tonyxforce/LynxSchematic/pcb/3v3.kicad_sch

## KiCad design pcb/3v3.kicad_sch (2026-06-30)

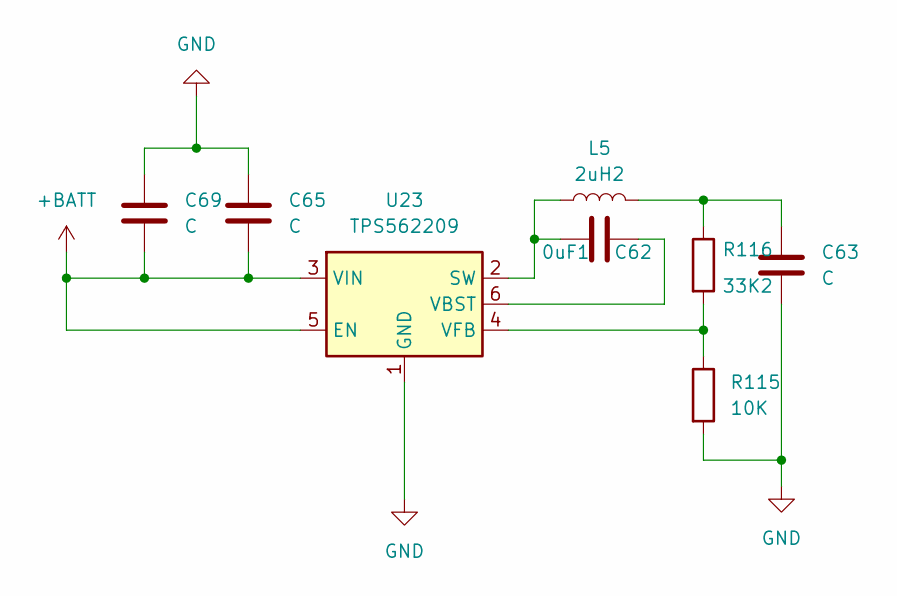
[picture p4: schematic 3v3.kicad_sch]

Parts:
C62: 0uF1
C63, C65, C69: C
L5: 2uH2
R115: 10K
R116: 33K2
U23: TPS562209; SOT-23-6

Connections:
+BATT: C65.2, C69.2, U23.3 (VIN), U23.5 (EN)
GND: C63.2, C65.1, C69.1, R115.2, U23.1 (GND)
unnamed: C62.1, L5.1, U23.2 (SW)
unnamed: C62.2, U23.6 (VBST)
unnamed: C63.1, L5.2, R116.1
unnamed: R115.1, R116.2, U23.4 (VFB)
