tonyxforce/LynxSchematic/pcb/5v.kicad_sch

## KiCad design pcb/5v.kicad_sch (2026-06-30)

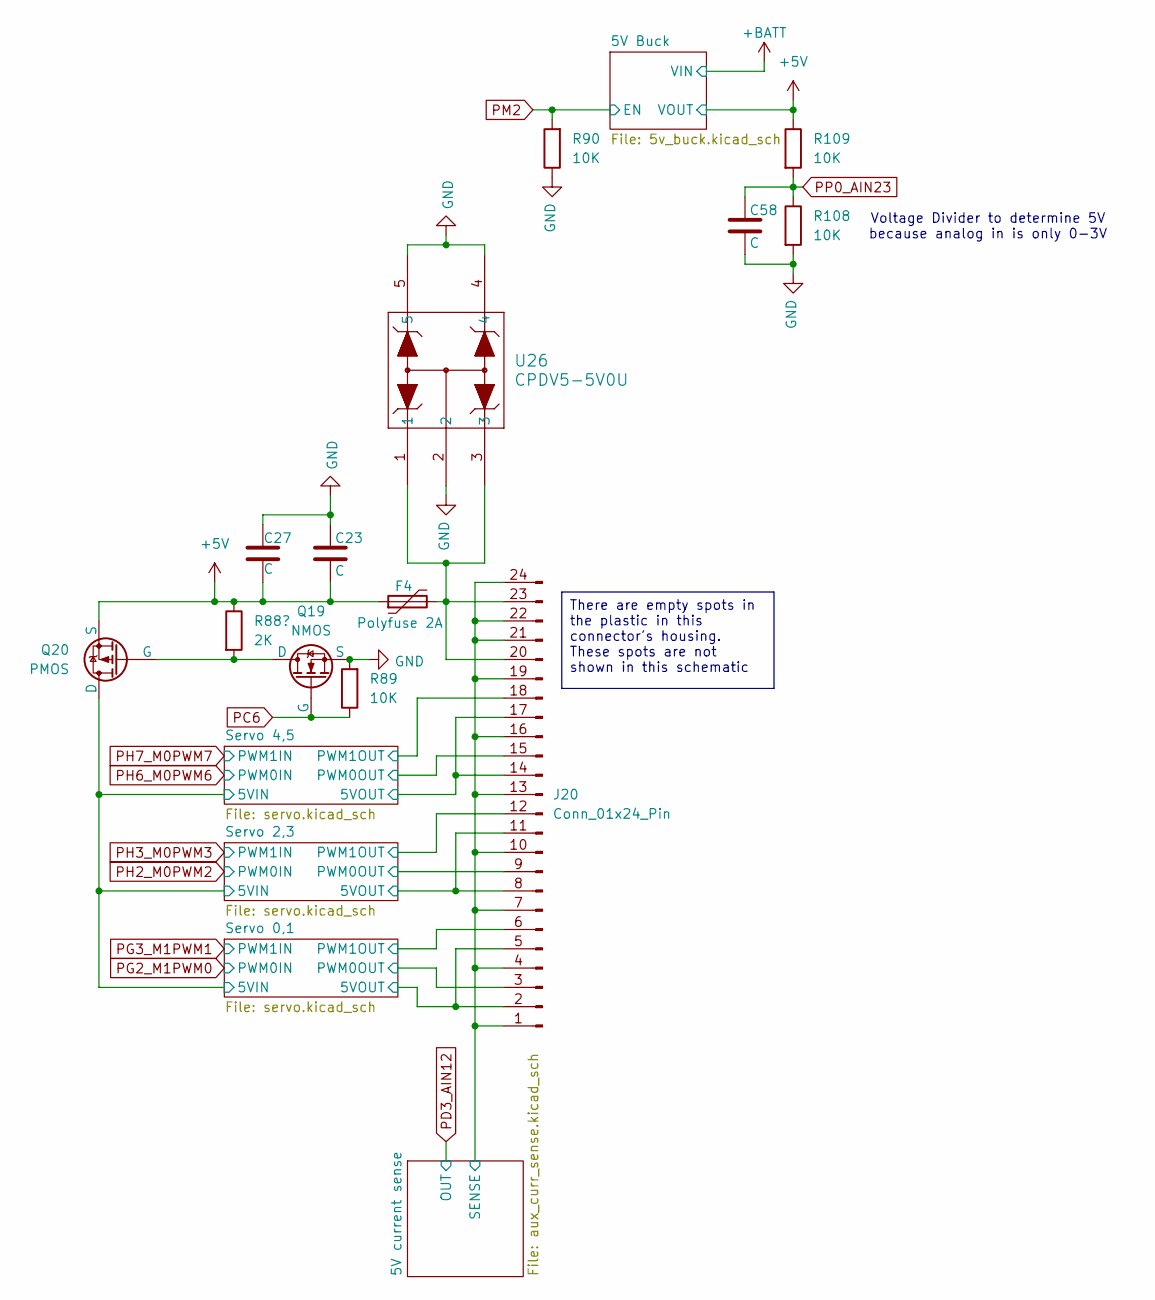
[picture p5: schematic 5v.kicad_sch]

Parts:
C23, C27, C58: C
F4: Polyfuse 2A
J20: Conn_01x24_Pin
Q19: NMOS
Q20: PMOS
R89, R90, R108, R109: 10K
U26: CPDV5-5V0U; SOT353_CPDV5_CIP

Connections:
5VIN: Q20.1 (D)
5VOUT: J20.2, J20.5, J20.8, J20.11, J20.14, J20.17
+5V: C23.2, C27.1, F4.1, Q20.3 (S), R109.1
GND: C23.1, C27.2, C58.2, Q19.3 (S), R89.2, R90.1, R108.2, U26.2, U26.4, U26.5
unnamed: F4.2, J20.20, J20.23, U26.1, U26.3
unnamed: Q19.1 (D), Q20.2 (G)
PC6: Q19.2 (G), R89.1
PM2: R90.2
PP0_AIN23: C58.1, R108.1, R109.2
PWM0OUT: J20.3, J20.9, J20.15
PWM1OUT: J20.6, J20.12, J20.18
SENSE: J20.1, J20.4, J20.7, J20.10, J20.13, J20.16, J20.19, J20.21, J20.22, J20.24

Notes on the sheet:
Voltage Divider to determine 5V because analog in is only 0-3V
There are empty spots in the plastic in this connector's housing. These spots are not shown in this schematic
