tonyxforce/LynxSchematic/pcb/5v_buck.kicad_sch

## KiCad design pcb/5v_buck.kicad_sch (2026-06-30)

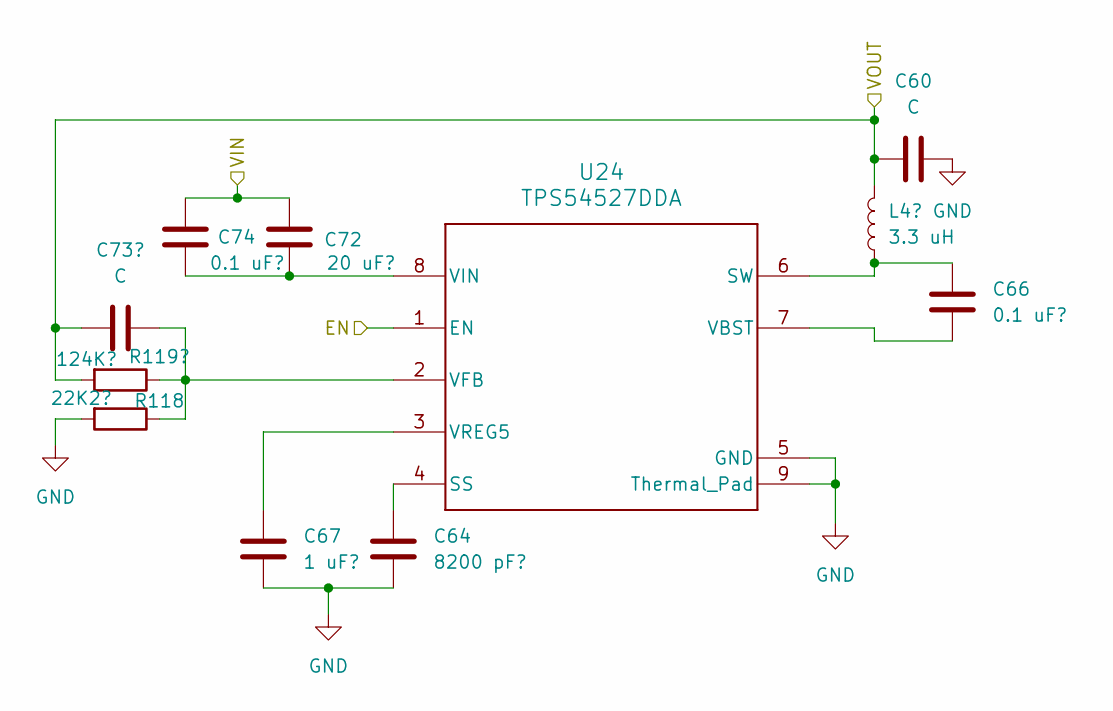
[picture p6: schematic 5v_buck.kicad_sch]

Parts:
C60: C
C64: 8200 pF?
C66, C74: 0.1 uF?
C67: 1 uF?
C72: 20 uF?
R118: 22K2?
U24: TPS54527DDA; DDA0008E-IPC_A

Connections:
EN: U24.1 (EN)
GND: C60.2, C64.2, C67.2, R118.2, U24.5 (GND), U24.9 (Thermal_Pad)
unnamed: C64.1, U24.4 (SS)
unnamed: C66.1, U24.6 (SW)
unnamed: C66.2, U24.7 (VBST)
unnamed: C67.1, U24.3 (VREG5)
unnamed: C72.2, C74.2, U24.8 (VIN)
unnamed: R118.1, U24.2 (VFB)
VIN: C72.1, C74.1
VOUT: C60.1
