tonyxforce/LynxSchematic/pcb/12v.kicad_sch

## KiCad design pcb/12v.kicad_sch (2026-06-30)

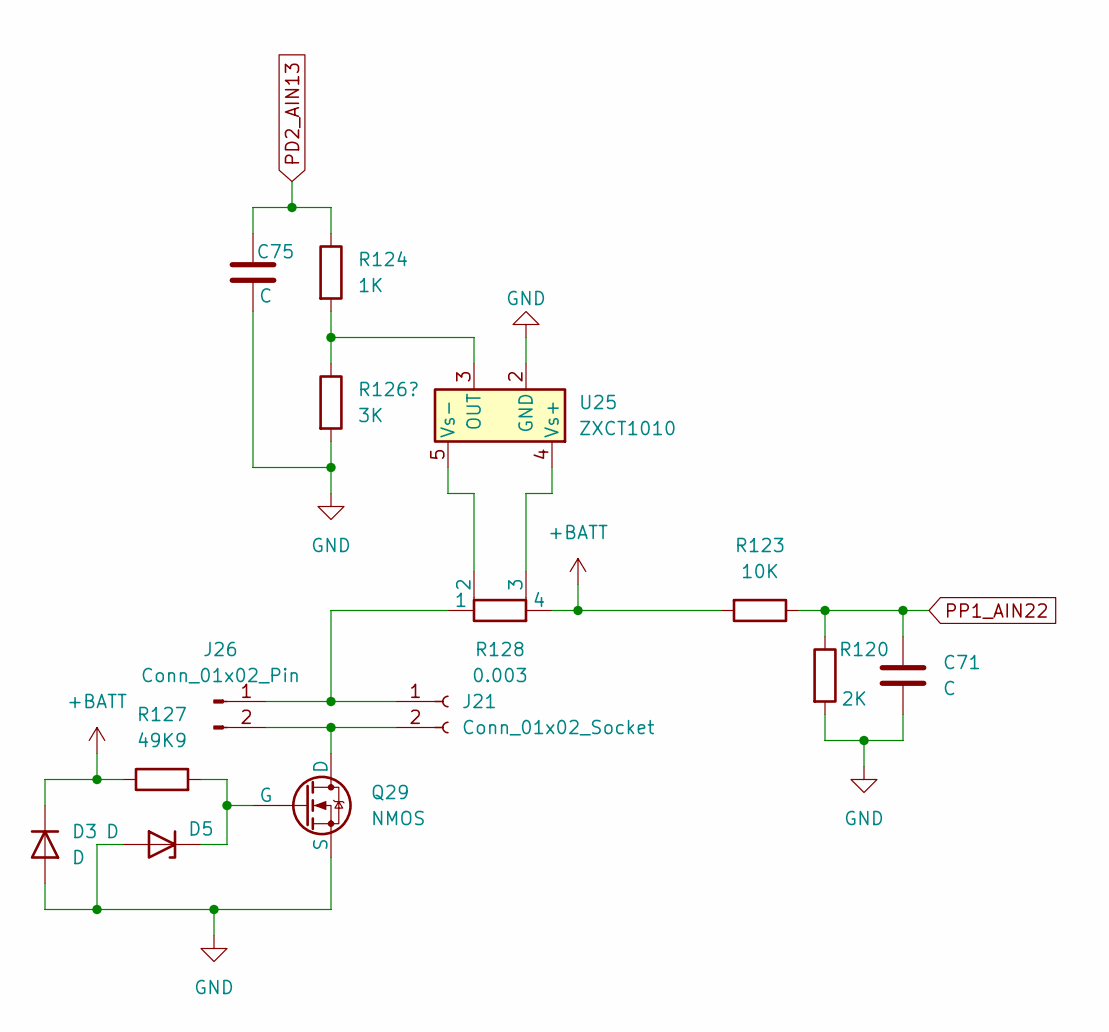
[picture p7: schematic 12v.kicad_sch]

Parts:
C71, C75: C
D3: D
D5: D; D_SOD-882
J21: Conn_01x02_Socket
J26: Conn_01x02_Pin
Q29: NMOS
R120: 2K
R123: 10K
R124: 1K
R127: 49K9
R128: 0.003
U25: ZXCT1010; SOT-23-5

Connections:
+BATT: D3.1 (K), R123.2, R127.1, R128.4
GND: C71.2, C75.1, D3.2 (A), D5.2 (A), Q29.3 (S), R120.2, U25.2 (GND)
unnamed: D5.1 (K), Q29.2 (G), R127.2
unnamed: J21.1, J26.1, R128.1
unnamed: J21.2, J26.2, Q29.1 (D)
unnamed: R124.2, U25.3 (OUT)
unnamed: R128.2, U25.5 (Vs-)
unnamed: R128.3, U25.4 (Vs+)
PD2_AIN13: C75.2, R124.1
PP1_AIN22: C71.1, R120.1, R123.1
