tonyxforce/LynxSchematic/pcb/analog_in_connector.kicad_sch

## KiCad design pcb/analog_in_connector.kicad_sch (2026-06-30)

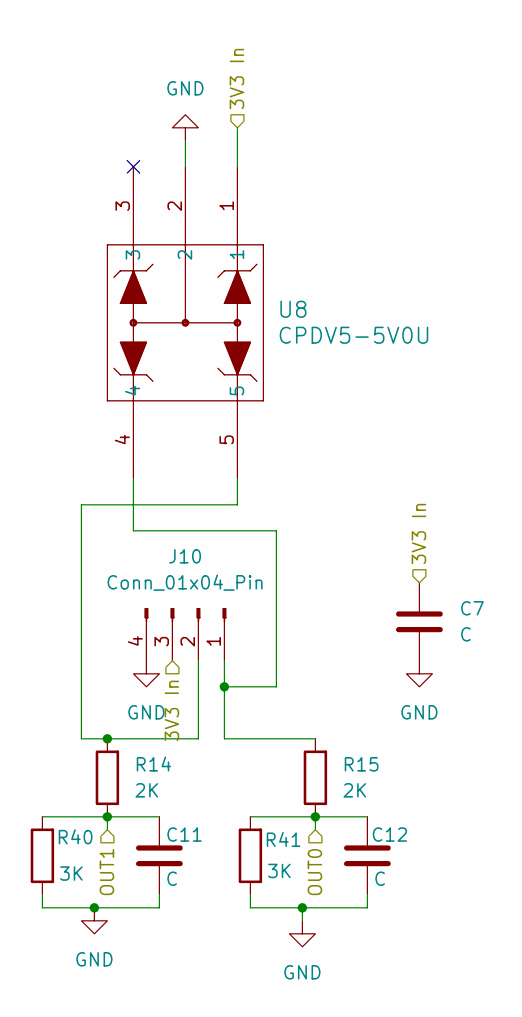
[picture p8: schematic analog_in_connector.kicad_sch]

Parts:
C7, C11, C12: C
J10: Conn_01x04_Pin
R14, R15: 2K
R40, R41: 3K
U8: CPDV5-5V0U; SOT353_CPDV5_CIP

Connections:
3V3 In: C7.1, J10.3, U8.1
GND: C7.2, C11.2, C12.2, J10.4, R40.1, R41.1, U8.2
unnamed: J10.1, R15.2, U8.4
unnamed: J10.2, R14.2, U8.5
OUT0: C12.1, R15.1, R41.2
OUT1: C11.1, R14.1, R40.2
