tonyxforce/LynxSchematic/pcb/android_header.kicad_sch

## KiCad design pcb/android_header.kicad_sch (2026-06-30)

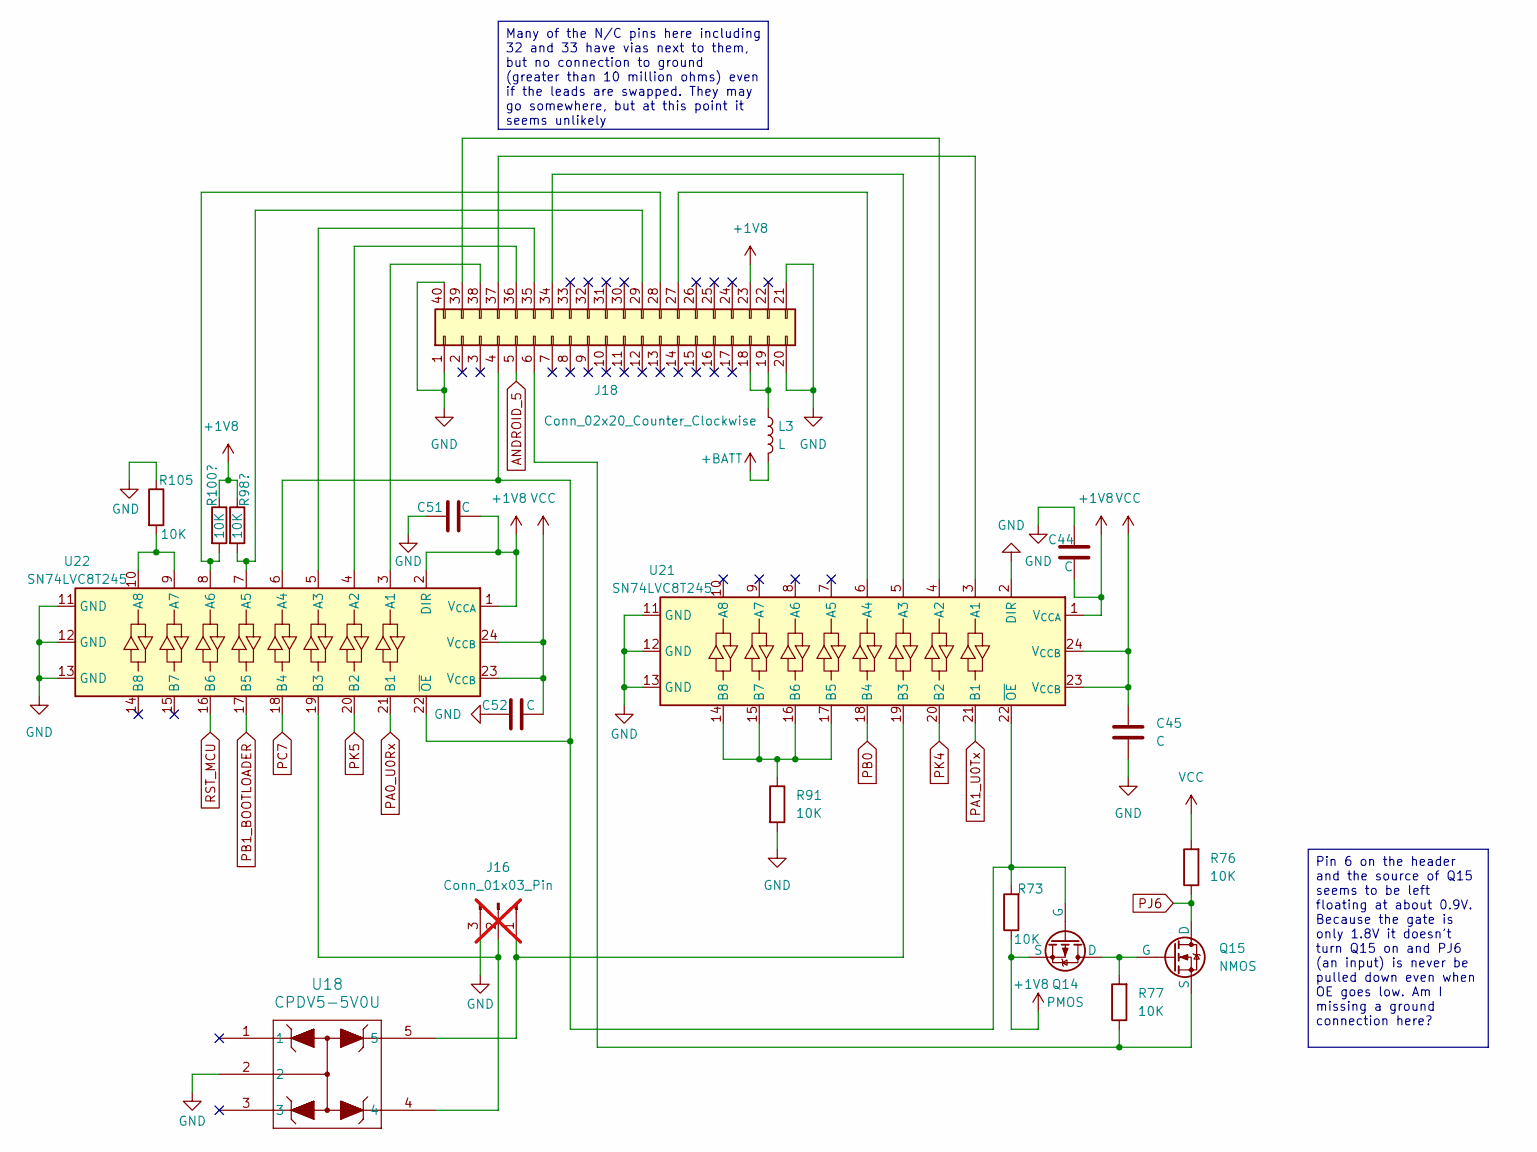
[picture p9: schematic android_header.kicad_sch]

Parts:
C44, C45, C51, C52: C
J16: Conn_01x03_Pin; not fitted
J18: Conn_02x20_Counter_Clockwise
L3: L
Q14: PMOS
Q15: NMOS
R73, R76, R77, R91, R105: 10K
U18: CPDV5-5V0U; SOT353_CPDV5_CIP
U21, U22: SN74LVC8T245

Connections:
+1V8: C44.2, C51.2, J18.23, Q14.3 (S), R73.1, U21.1 (V_{CCA}), U22.1 (V_{CCA}), U22.2 (DIR)
+BATT: L3.2
ANDROID_5: J18.5
GND: C44.1, C45.2, C51.1, C52.1, J16.3, J18.1, J18.20, J18.21, J18.40, R91.2, R105.1, U18.2, U21.2 (DIR), U21.11 (GND), U21.12 (GND), U21.13 (GND), U22.11 (GND), U22.12 (GND), U22.13 (GND)
unnamed: J16.1, U18.5, U21.19 (B3)
unnamed: J16.2, U18.4, U22.19 (B3)
unnamed: J18.4, Q14.2 (G), R73.2, U21.22 (~OE), U22.6 (A4), U22.22 (~OE)
unnamed: J18.6, Q15.3 (S), R77.1
unnamed: J18.18, J18.19, L3.1
unnamed: J18.27, U21.6 (A4)
unnamed: J18.28, U22.8 (A6)
unnamed: J18.29, U22.7 (A5)
unnamed: J18.34, U21.5 (A3)
unnamed: J18.35, U22.5 (A3)
unnamed: J18.36, U22.4 (A2)
unnamed: J18.37, U21.3 (A1)
unnamed: J18.38, U22.3 (A1)
unnamed: J18.39, U21.4 (A2)
unnamed: Q14.1 (D), Q15.2 (G), R77.2
unnamed: R91.1, U21.14 (B8), U21.15 (B7), U21.16 (B6), U21.17 (B5)
unnamed: R105.2, U22.9 (A7), U22.10 (A8)
PA0_U0Rx: U22.21 (B1)
PA1_U0Tx: U21.21 (B1)
PB0: U21.18 (B4)
PB1_BOOTLOADER: U22.17 (B5)
PC7: U22.18 (B4)
PJ6: Q15.1 (D), R76.1
PK4: U21.20 (B2)
PK5: U22.20 (B2)
RST_MCU: U22.16 (B6)
VCC: C45.1, C52.2, R76.2, U21.23 (V_{CCB}), U21.24 (V_{CCB}), U22.23 (V_{CCB}), U22.24 (V_{CCB})

Notes on the sheet:
Many of the N/C pins here including 32 and 33 have vias next to them, but no connection to ground (greater than 10 million ohms) even if the leads are swapped. They may go somewhere, but at this point it seems unlikely
Pin 6 on the header and the source of Q15 seems to be left floating at about 0.9V. Because the gate is only 1.8V it doesn't turn Q15 on and PJ6 (an input) is never be pulled down even when OE goes low. Am I missing a ground connection here?
