tonyxforce/LynxSchematic/pcb/aux_curr_sense.kicad_sch

## KiCad design pcb/aux_curr_sense.kicad_sch (2026-06-30)

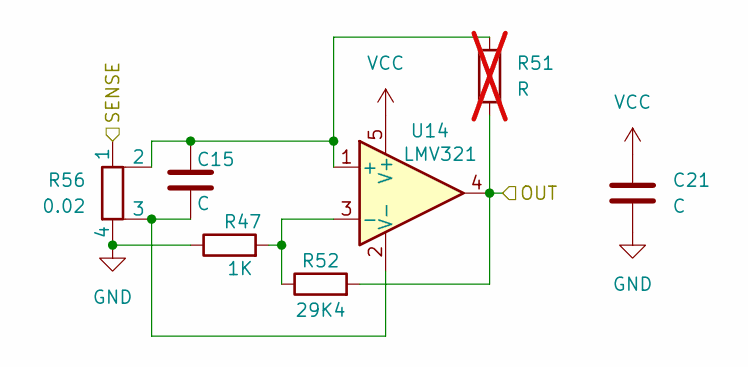
[picture p10: schematic aux_curr_sense.kicad_sch]

Parts:
C15, C21: C
R47: 1K; R_0603_1608Metric
R51: R; R_0603_1608Metric; not fitted
R52: 29K4; R_0603_1608Metric
R56: 0.02; R_Shunt_Vishay_WSK2512_6332Metric_T1.19mm
U14: LMV321; SOT-23-5

Connections:
GND: C21.2, R47.1, R56.4
unnamed: C15.1, R51.2, R56.2, U14.1 (+)
unnamed: C15.2, R56.3, U14.2 (V-)
unnamed: R47.2, R52.1, U14.3 (-)
OUT: R51.1, R52.2, U14.4
SENSE: R56.1
VCC: C21.1, U14.5 (V+)
