tonyxforce/LynxSchematic/pcb/button.kicad_sch

## KiCad design pcb/button.kicad_sch (2026-06-30)

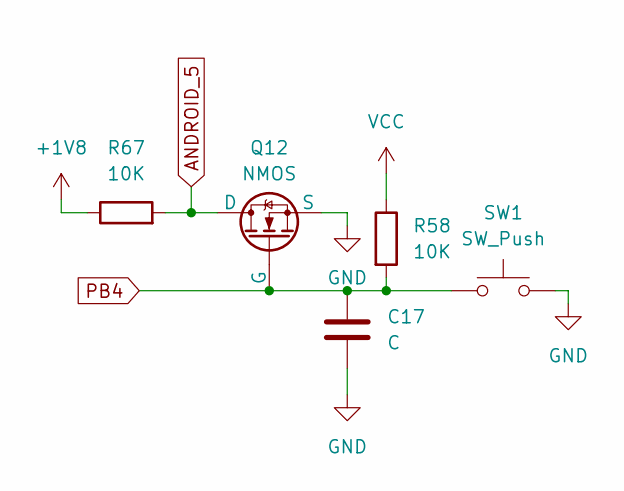
[picture p11: schematic button.kicad_sch]

Parts:
C17: C
Q12: NMOS
R58, R67: 10K
SW1: SW_Push

Connections:
+1V8: R67.1
ANDROID_5: Q12.1 (D), R67.2
GND: C17.2, Q12.3 (S), SW1.2
PB4: C17.1, Q12.2 (G), R58.2, SW1.1
VCC: R58.1
