tonyxforce/LynxSchematic/pcb/debug_uart.kicad_sch

## KiCad design pcb/debug_uart.kicad_sch (2026-06-30)

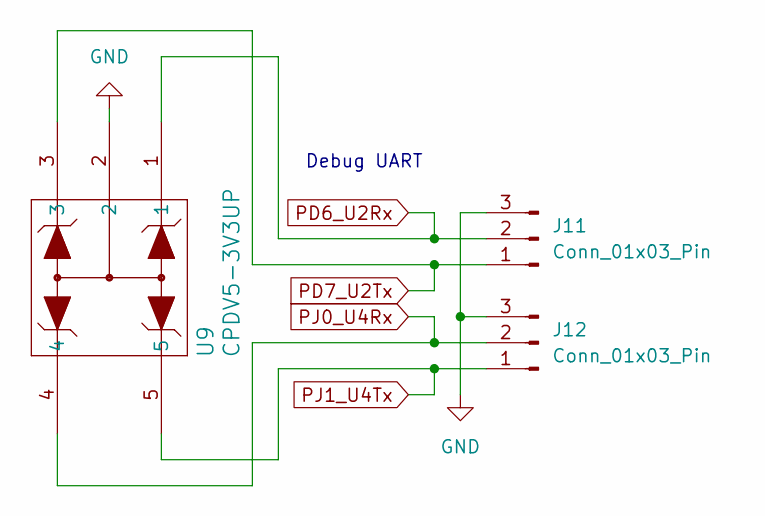
[picture p12: schematic debug_uart.kicad_sch]

Parts:
J11, J12: Conn_01x03_Pin
U9: CPDV5-3V3UP; SOT353_CPDV5_CIP

Connections:
GND: J11.3, J12.3, U9.2
PD6_U2Rx: J11.2, U9.1
PD7_U2Tx: J11.1, U9.3
PJ0_U4Rx: J12.2, U9.4
PJ1_U4Tx: J12.1, U9.5

Notes on the sheet:
Debug UART
