tonyxforce/LynxSchematic/pcb/encoder.kicad_sch

## KiCad design pcb/encoder.kicad_sch (2026-06-30)

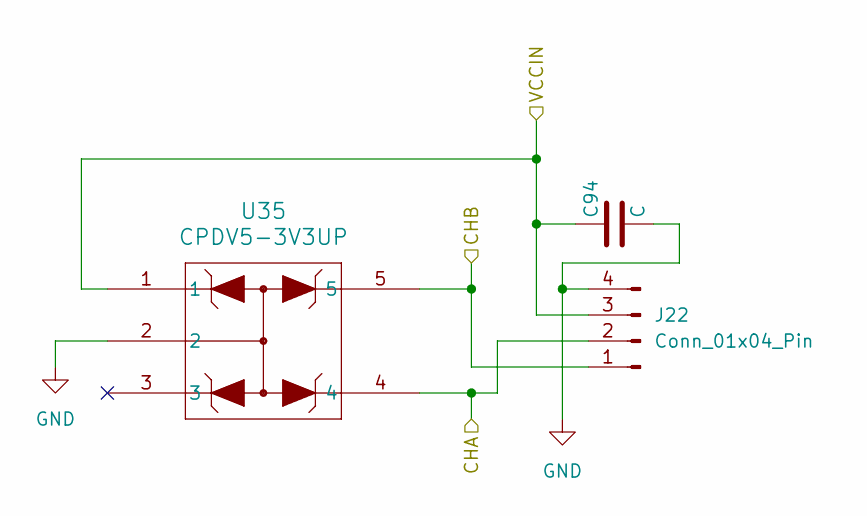
[picture p13: schematic encoder.kicad_sch]

Parts:
C94: C
J22: Conn_01x04_Pin
U35: CPDV5-3V3UP; SOT353_CPDV5_CIP

Connections:
CHA: J22.2, U35.4
CHB: J22.1, U35.5
GND: C94.1, J22.4, U35.2
VCCIN: C94.2, J22.3, U35.1
