tonyxforce/LynxSchematic/pcb/gpio.kicad_sch

## KiCad design pcb/gpio.kicad_sch (2026-06-30)

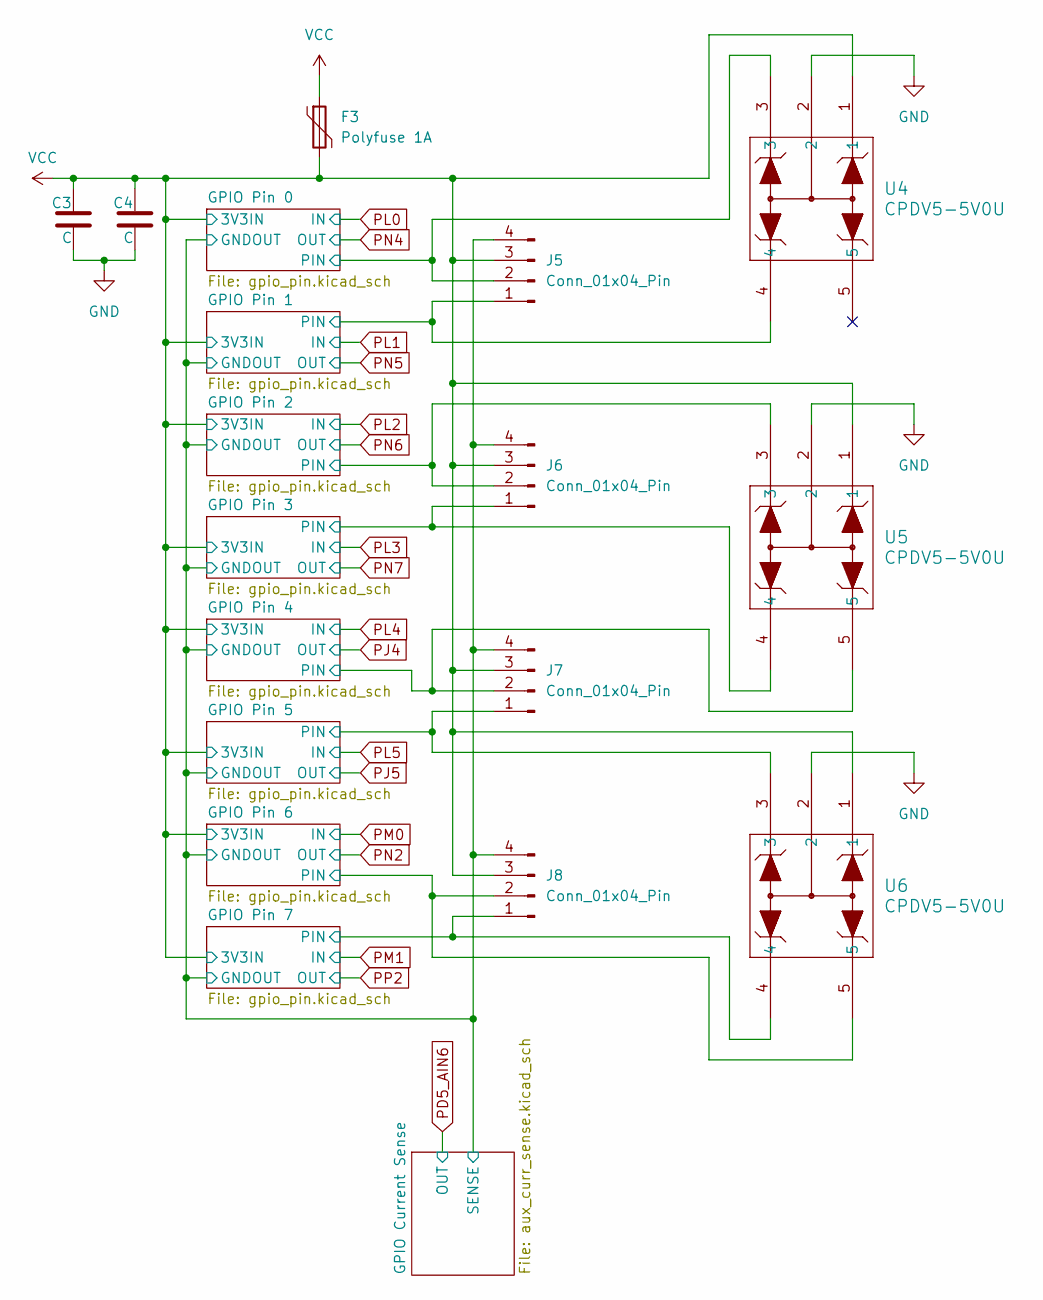
[picture p14: schematic gpio.kicad_sch]

Parts:
C3, C4: C
F3: Polyfuse 1A
J5, J6, J7, J8: Conn_01x04_Pin; JST_PH_B4B-PH-K_1x04_P2.00mm_Vertical
U4, U5, U6: CPDV5-5V0U; SOT353_CPDV5_CIP

Connections:
GND: C3.2, C4.2, U4.2, U5.2, U6.2
GNDOUT: J5.4, J6.4, J7.4, J8.4
PIN: J5.1, J5.2, J6.1, J6.2, J7.1, J7.2, J8.1, J8.2, U4.3, U4.4, U5.3, U5.4, U5.5, U6.3, U6.4, U6.5
VCC: C3.1, C4.1, F3.1, F3.2, J5.3, J6.3, J7.3, J8.3, U4.1, U5.1, U6.1
