tonyxforce/LynxSchematic/pcb/gpio_pin.kicad_sch

## KiCad design pcb/gpio_pin.kicad_sch (2026-06-30)

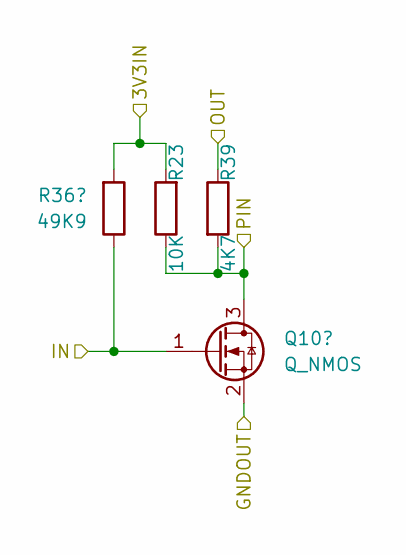
[picture p15: schematic gpio_pin.kicad_sch]

Parts:
R23: 10K; R_0603_1608Metric
R34: 49K9; R_0603_1608Metric
R39: 4K7; R_0603_1608Metric

Connections:
3V3IN: R23.2, R34.2
IN: R34.1
OUT: R39.1
PIN: R23.1, R39.2
