tonyxforce/LynxSchematic/pcb/i2c.kicad_sch

## KiCad design pcb/i2c.kicad_sch (2026-06-30)

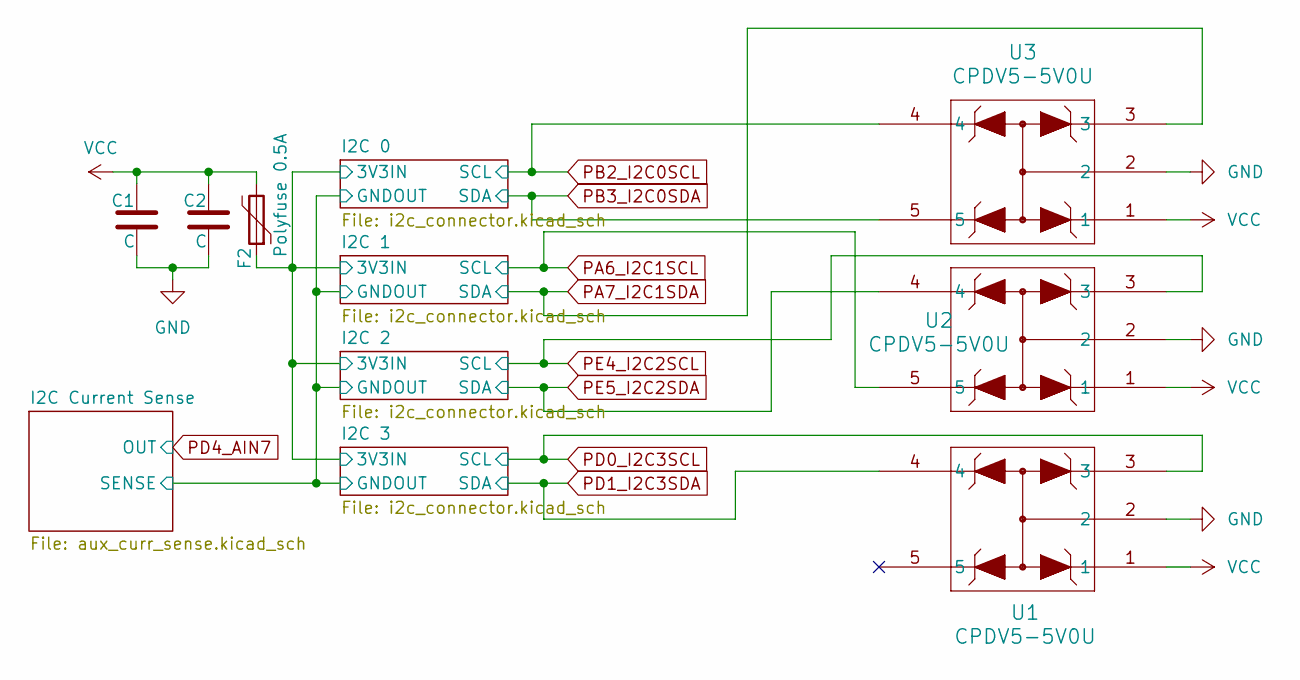
[picture p16: schematic i2c.kicad_sch]

Parts:
C1, C2: C
F2: Polyfuse 0.5A
U1, U2, U3: CPDV5-5V0U; SOT353_CPDV5_CIP

Connections:
3V3IN: F2.1
GND: C1.2, C2.2, U1.2, U2.2, U3.2
PA6_I2C1SCL: U2.5
PA7_I2C1SDA: U3.3
PB2_I2C0SCL: U3.4
PB3_I2C0SDA: U3.5
PD0_I2C3SCL: U1.3
PD1_I2C3SDA: U1.4
PE4_I2C2SCL: U2.3
PE5_I2C2SDA: U2.4
VCC: C1.1, C2.1, F2.2, U1.1, U2.1, U3.1
