tonyxforce/LynxSchematic/pcb/i2c_connector.kicad_sch

## KiCad design pcb/i2c_connector.kicad_sch (2026-06-30)

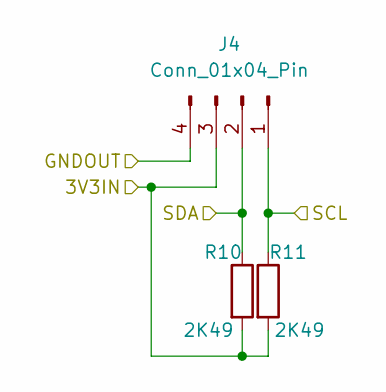
[picture p17: schematic i2c_connector.kicad_sch]

Parts:
J4: Conn_01x04_Pin
R10, R11: 2K49

Connections:
3V3IN: J4.3, R10.2, R11.2
GNDOUT: J4.4
SCL: J4.1, R11.1
SDA: J4.2, R10.1
