tonyxforce/LynxSchematic/pcb/imu.kicad_sch

## KiCad design pcb/imu.kicad_sch (2026-06-30)

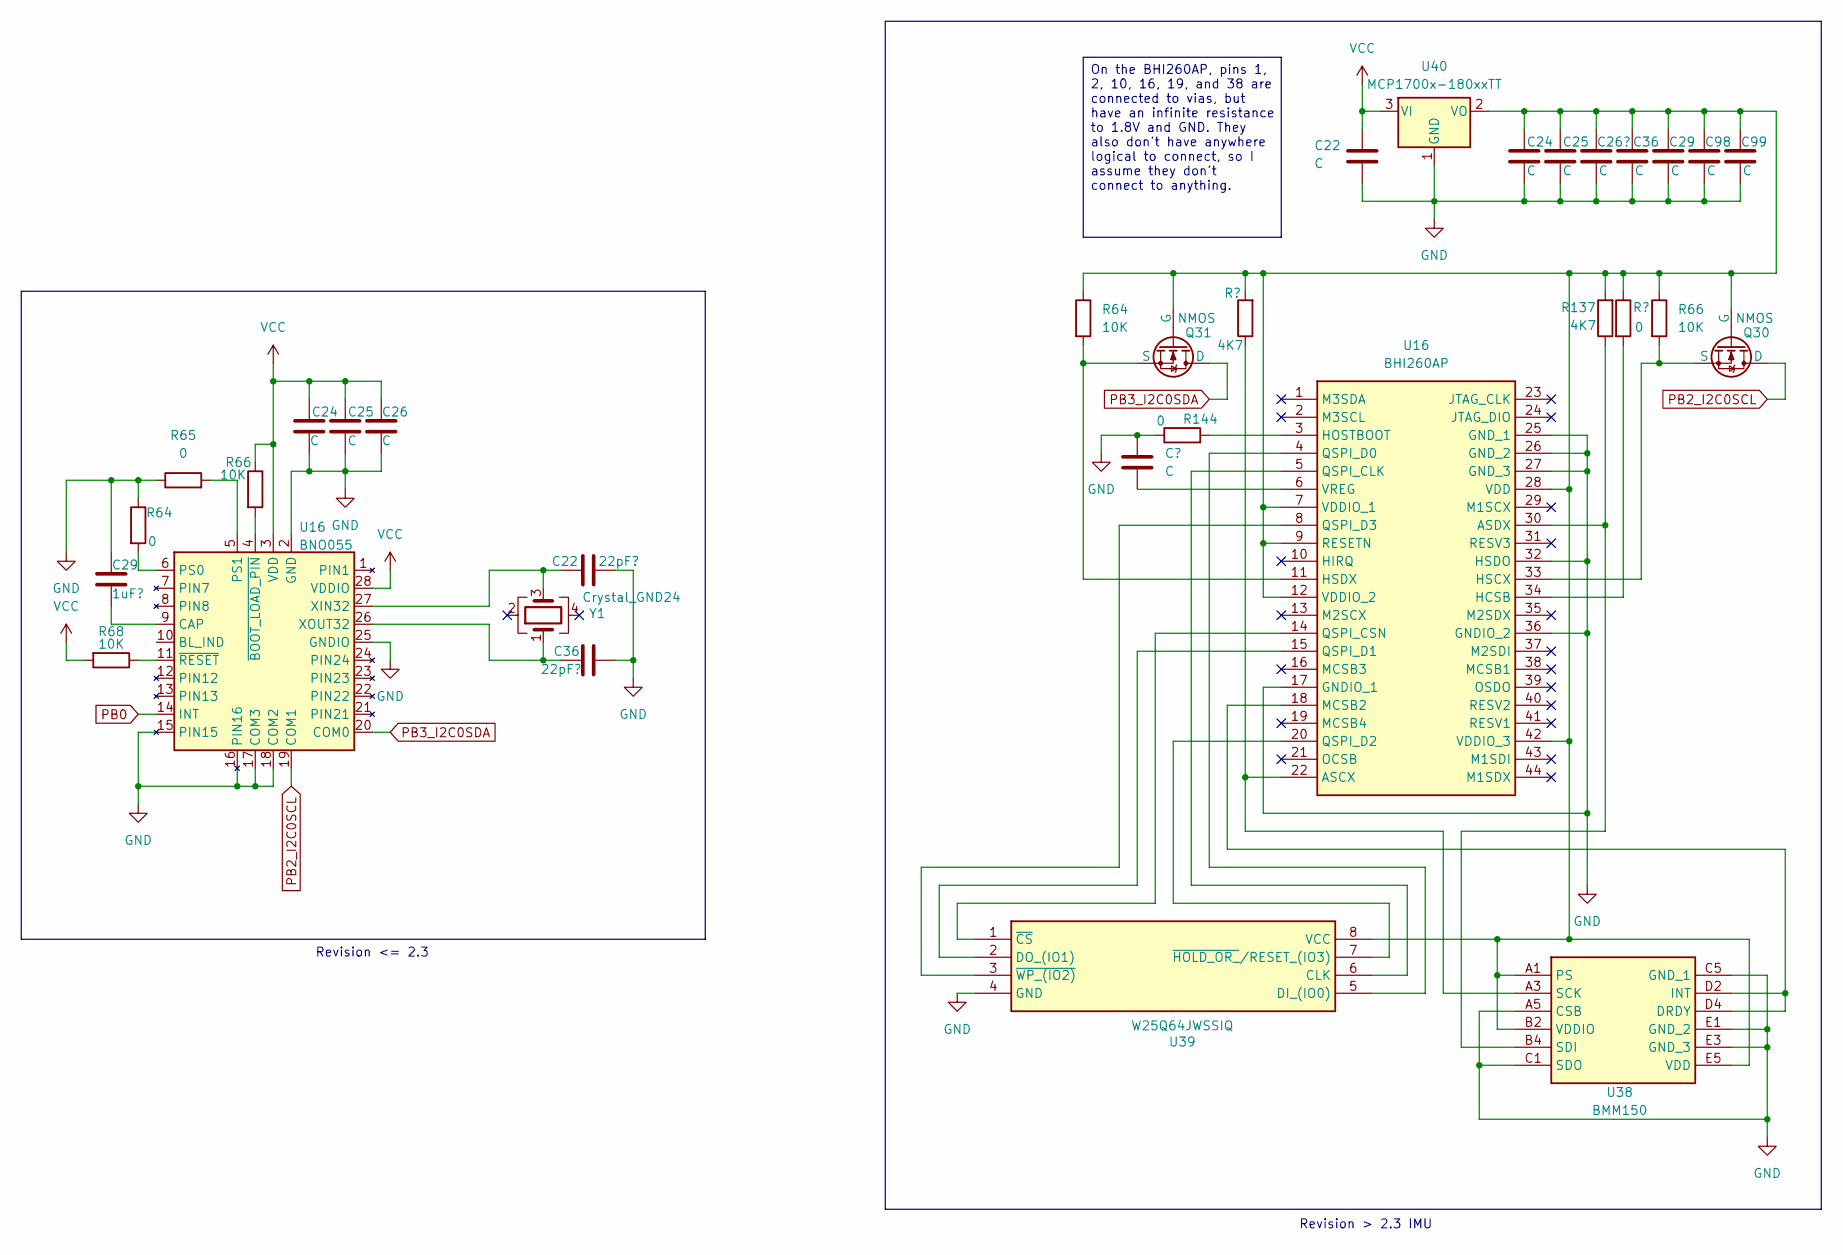
[picture p18: schematic imu.kicad_sch]

Parts:
C22, C24, C25, C26, C29, C98, C99: C
C36: 22pF?
Q30, Q31: NMOS
R64, R65, R144: 0
R66, R68: 10K
R137: 4K7
U16: BHI260AP; Mouser Part Number 262-BHI260AP
U38: BMM150; Mouser Part Number 262-BMM150
U39: W25Q64JWSSIQ; SOIC127P790X216-8N; Mouser Part Number 454-W25Q64JWSSIQ
U40: MCP1700x-180xxTT; SOT-23
Y1: Crystal_GND24

Connections:
GND: C22.2, C24.2, C25.2, C26.2, C29.1, C29.2, C36.2, C98.2, C99.2, R64.1, R65.1, R144.1, U16.2 (GND), U16.15 (PIN15), U16.16 (PIN16), U16.17 (COM3), U16.18 (COM2), U16.25 (GNDIO), U16.26 (XOUT32), U16.27 (XIN32), U16.32 (HSDO), U16.36 (GNDIO_2), U38.A5 (CSB), U38.C1 (SDO), U38.C5 (GND_1), U38.E1 (GND_2), U38.E3 (GND_3), U39.4 (GND), U40.1 (GND)
unnamed: C22.1, U16.27 (XIN32), Y1.3
unnamed: C24.1, C25.1, C29.1, C36.1, C98.1, C99.1, Q30.2 (G), Q31.2 (G), R64.1, R66.1, R137.2, U16.7 (PIN7), U16.9 (CAP), U16.12 (PIN12), U16.28 (VDDIO), U16.42 (VDDIO_3), U38.A1 (PS), U38.B2 (VDDIO), U38.E5 (VDD), U39.8 (VCC), U40.2 (VO)
unnamed: C29.2, U16.9 (CAP)
unnamed: C36.1, U16.26 (XOUT32), Y1.1
unnamed: Q30.3 (S), R66.2, U16.33 (HSCX)
unnamed: Q31.3 (S), R64.2, U16.11 (~RESET)
unnamed: R64.2, U16.6 (PS0)
unnamed: R65.2, U16.5 (PS1)
unnamed: R66.2, U16.4 (~BOOT_LOAD_PIN)
unnamed: R68.1, U16.11 (~RESET)
unnamed: R137.1, U16.30 (ASDX), U38.B4 (SDI)
unnamed: R144.2, U16.3 (VDD)
unnamed: U16.4 (~BOOT_LOAD_PIN), U39.5 (DI_(IO0))
unnamed: U16.5 (PS1), U39.6 (CLK)
unnamed: U16.8 (PIN8), U39.3 (~WP_(IO2))
unnamed: U16.14 (INT), U39.1 (~CS)
unnamed: U16.15 (PIN15), U39.2 (DO_(IO1))
unnamed: U16.18 (COM2), U38.D2 (INT), U38.D4 (DRDY)
unnamed: U16.20 (COM0), U39.7 (~HOLD_OR_/RESET_(IO3))
unnamed: U16.22 (PIN22), U38.A3 (SCK)
PB0: U16.14 (INT)
PB2_I2C0SCL: Q30.1 (D), U16.19 (COM1)
PB3_I2C0SDA: Q31.1 (D), U16.20 (COM0)
VCC: C22.1, C24.1, C25.1, C26.1, R66.1, R68.2, U16.3 (VDD), U16.28 (VDDIO), U40.3 (VI)

Notes on the sheet:
Revision <= 2.3
Revision > 2.3 IMU
On the BHI260AP, pins 1, 2, 10, 16, 19, and 38 are connected to vias, but have an infinite resistance to 1.8V and GND. They also don't have anywhere logical to connect, so I assume they don't connect to anything.
