tonyxforce/LynxSchematic/pcb/led.kicad_sch

## KiCad design pcb/led.kicad_sch (2026-06-30)

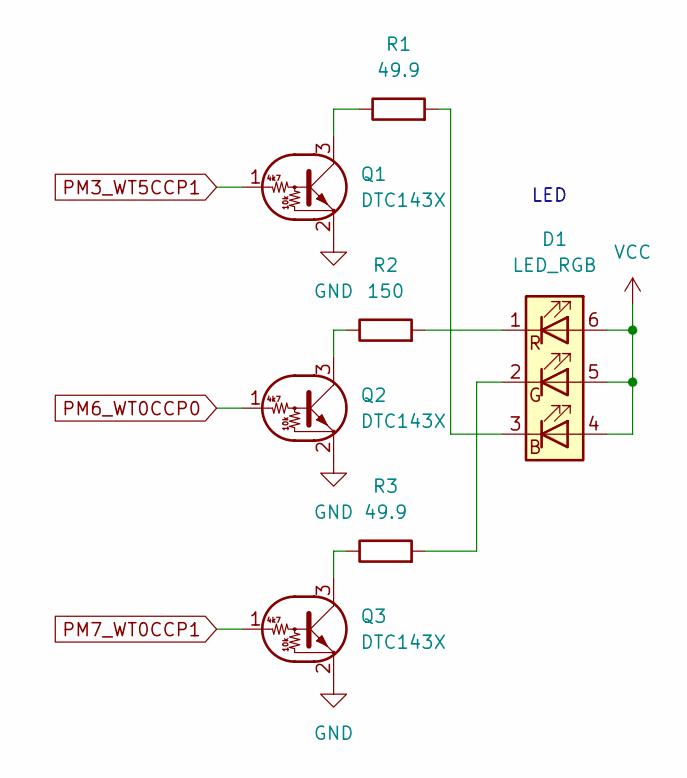
[picture p19: schematic led.kicad_sch]

Parts:
D1: LED_RGB
Q1, Q2, Q3: DTC143X
R1, R3: 49.9
R2: 150

Connections:
GND: Q1.2 (E), Q2.2 (E), Q3.2 (E)
unnamed: D1.1 (RK), R2.2
unnamed: D1.2 (GK), R3.2
unnamed: D1.3 (BK), R1.2
unnamed: Q1.3 (C), R1.1
unnamed: Q2.3 (C), R2.1
unnamed: Q3.3 (C), R3.1
PM3_WT5CCP1: Q1.1 (B)
PM6_WT0CCP0: Q2.1 (B)
PM7_WT0CCP1: Q3.1 (B)
VCC: D1.4 (BA), D1.5 (GA), D1.6 (RA)

Notes on the sheet:
LED
