tonyxforce/LynxSchematic/pcb/mcu.kicad_sch

## KiCad design pcb/mcu.kicad_sch (2026-06-30)

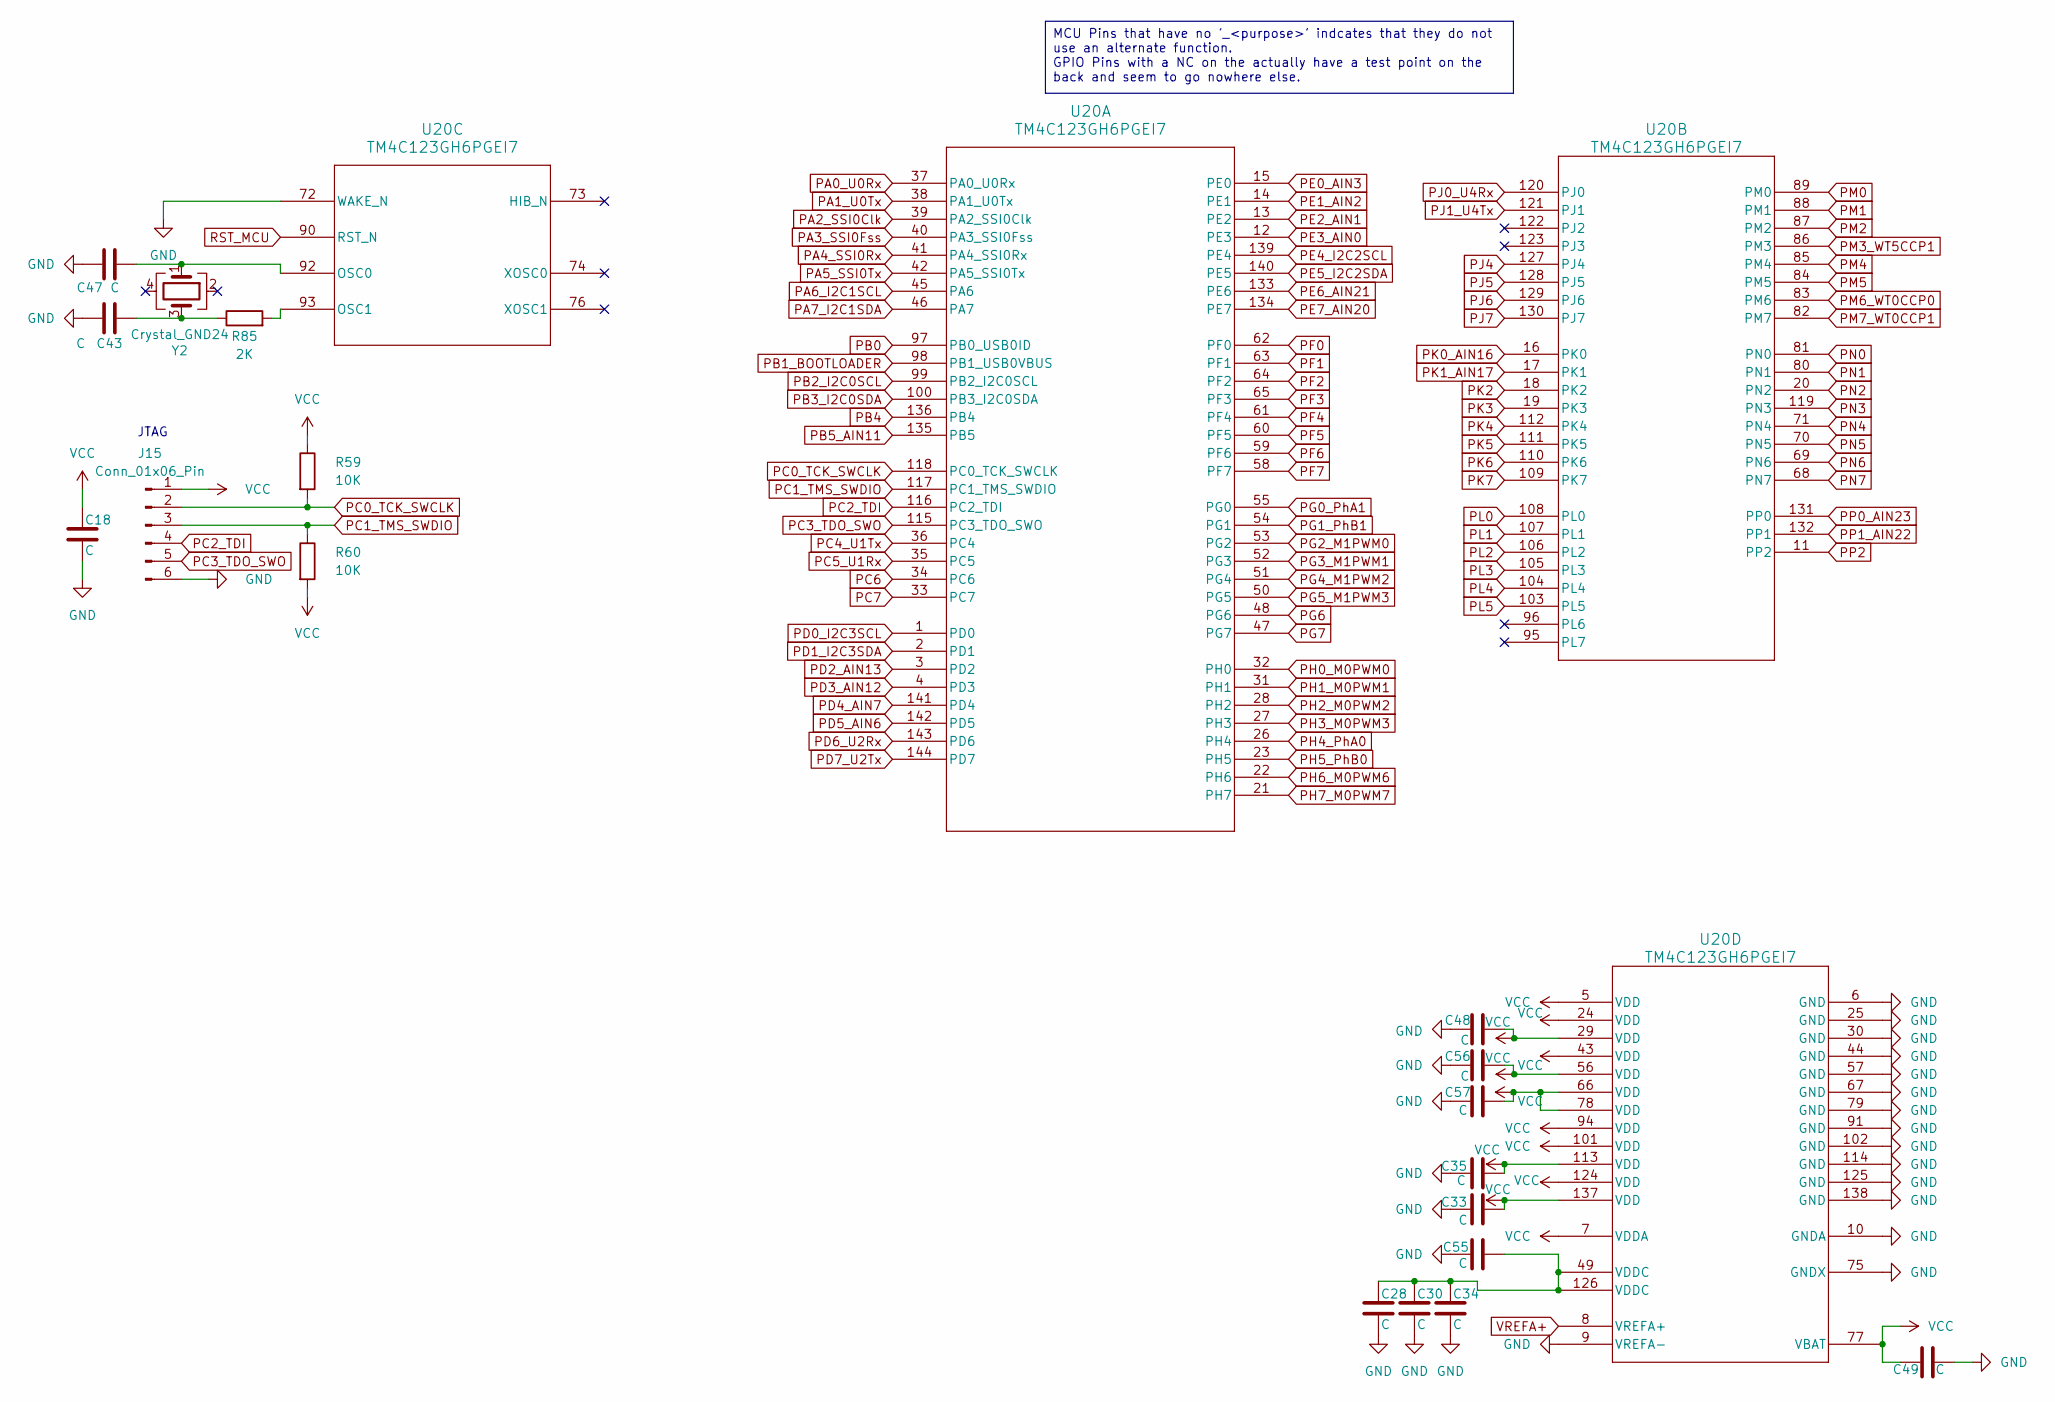
[picture p20: schematic mcu.kicad_sch]

Parts:
C18, C28, C30, C33, C34, C35, C43, C47, C48, C49, C55, C56, C57: C
J15: Conn_01x06_Pin
R59, R60: 10K
R85: 2K
U20: TM4C123GH6PGEI7; PGE0144A_N
Y2: Crystal_GND24

Connections:
GND: C18.1, C28.2, C30.2, C33.2, C34.2, C35.2, C43.2, C47.2, C48.2, C49.2, C55.2, C56.2, C57.2, J15.6, U20.6 (GND), U20.9 (VREFA-), U20.10 (GNDA), U20.25 (GND), U20.30 (GND), U20.44 (GND), U20.57 (GND), U20.67 (GND), U20.72 (WAKE_N), U20.75 (GNDX), U20.79 (GND), U20.91 (GND), U20.102 (GND), U20.114 (GND), U20.125 (GND), U20.138 (GND)
unnamed: C28.1, C30.1, C34.1, C55.1, U20.49 (VDDC), U20.126 (VDDC)
unnamed: C43.1, R85.1, Y2.3
unnamed: C47.1, U20.92 (OSC0), Y2.1
unnamed: R85.2, U20.93 (OSC1)
PA0_U0Rx: U20.37 (PA0_U0Rx)
PA1_U0Tx: U20.38 (PA1_U0Tx)
PA2_SSI0Clk: U20.39 (PA2_SSI0Clk)
PA3_SSI0Fss: U20.40 (PA3_SSI0Fss)
PA4_SSI0Rx: U20.41 (PA4_SSI0Rx)
PA5_SSI0Tx: U20.42 (PA5_SSI0Tx)
PA6_I2C1SCL: U20.45 (PA6)
PA7_I2C1SDA: U20.46 (PA7)
PB0: U20.97 (PB0_USB0ID)
PB1_BOOTLOADER: U20.98 (PB1_USB0VBUS)
PB2_I2C0SCL: U20.99 (PB2_I2C0SCL)
PB3_I2C0SDA: U20.100 (PB3_I2C0SDA)
PB4: U20.136 (PB4)
PB5_AIN11: U20.135 (PB5)
PC0_TCK_SWCLK: J15.2, R59.2, U20.118 (PC0_TCK_SWCLK)
PC1_TMS_SWDIO: J15.3, R60.1, U20.117 (PC1_TMS_SWDIO)
PC2_TDI: J15.4, U20.116 (PC2_TDI)
PC3_TDO_SWO: J15.5, U20.115 (PC3_TDO_SWO)
PC4_U1Tx: U20.36 (PC4)
PC5_U1Rx: U20.35 (PC5)
PC6: U20.34 (PC6)
PC7: U20.33 (PC7)
PD0_I2C3SCL: U20.1 (PD0)
PD1_I2C3SDA: U20.2 (PD1)
PD2_AIN13: U20.3 (PD2)
PD3_AIN12: U20.4 (PD3)
PD4_AIN7: U20.141 (PD4)
PD5_AIN6: U20.142 (PD5)
PD6_U2Rx: U20.143 (PD6)
PD7_U2Tx: U20.144 (PD7)
PE0_AIN3: U20.15 (PE0)
PE1_AIN2: U20.14 (PE1)
PE2_AIN1: U20.13 (PE2)
PE3_AIN0: U20.12 (PE3)
PE4_I2C2SCL: U20.139 (PE4)
PE5_I2C2SDA: U20.140 (PE5)
PE6_AIN21: U20.133 (PE6)
PE7_AIN20: U20.134 (PE7)
PF0: U20.62 (PF0)
PF1: U20.63 (PF1)
PF2: U20.64 (PF2)
PF3: U20.65 (PF3)
PF4: U20.61 (PF4)
PF5: U20.60 (PF5)
PF6: U20.59 (PF6)
PF7: U20.58 (PF7)
PG0_PhA1: U20.55 (PG0)
PG1_PhB1: U20.54 (PG1)
PG2_M1PWM0: U20.53 (PG2)
PG3_M1PWM1: U20.52 (PG3)
PG4_M1PWM2: U20.51 (PG4)
PG5_M1PWM3: U20.50 (PG5)
PG6: U20.48 (PG6)
PG7: U20.47 (PG7)
PH0_M0PWM0: U20.32 (PH0)
PH1_M0PWM1: U20.31 (PH1)
PH2_M0PWM2: U20.28 (PH2)
PH3_M0PWM3: U20.27 (PH3)
PH4_PhA0: U20.26 (PH4)
PH5_PhB0: U20.23 (PH5)
PH6_M0PWM6: U20.22 (PH6)
PH7_M0PWM7: U20.21 (PH7)
PJ0_U4Rx: U20.120 (PJ0)
PJ1_U4Tx: U20.121 (PJ1)
PJ4: U20.127 (PJ4)
PJ5: U20.128 (PJ5)
PJ6: U20.129 (PJ6)
PJ7: U20.130 (PJ7)
PK0_AIN16: U20.16 (PK0)
PK1_AIN17: U20.17 (PK1)
PK2: U20.18 (PK2)
PK3: U20.19 (PK3)
PK4: U20.112 (PK4)
PK5: U20.111 (PK5)
PK6: U20.110 (PK6)
PK7: U20.109 (PK7)
PL0: U20.108 (PL0)
PL1: U20.107 (PL1)
PL2: U20.106 (PL2)
PL3: U20.105 (PL3)
PL4: U20.104 (PL4)
PL5: U20.103 (PL5)
PM0: U20.89 (PM0)
PM1: U20.88 (PM1)
PM2: U20.87 (PM2)
PM3_WT5CCP1: U20.86 (PM3)
PM4: U20.85 (PM4)
PM5: U20.84 (PM5)
PM6_WT0CCP0: U20.83 (PM6)
PM7_WT0CCP1: U20.82 (PM7)
PN0: U20.81 (PN0)
PN1: U20.80 (PN1)
PN2: U20.20 (PN2)
PN3: U20.119 (PN3)
PN4: U20.71 (PN4)
PN5: U20.70 (PN5)
PN6: U20.69 (PN6)
PN7: U20.68 (PN7)
PP0_AIN23: U20.131 (PP0)
PP1_AIN22: U20.132 (PP1)
PP2: U20.11 (PP2)
RST_MCU: U20.90 (RST_N)
VCC: C18.2, C33.1, C35.1, C48.1, C49.1, C56.1, C57.1, J15.1, R59.1, R60.2, U20.5 (VDD), U20.7 (VDDA), U20.24 (VDD), U20.29 (VDD), U20.43 (VDD), U20.56 (VDD), U20.66 (VDD), U20.77 (VBAT), U20.78 (VDD), U20.94 (VDD), U20.101 (VDD), U20.113 (VDD), U20.124 (VDD), U20.137 (VDD)
VREFA+: U20.8 (VREFA+)

Notes on the sheet:
JTAG
MCU Pins that have no '_<purpose>' indcates that they do not use an alternate function. GPIO Pins with a NC on the actually have a test point on the back and seem to go nowhere else.
