tonyxforce/LynxSchematic/pcb/motor.kicad_sch

## KiCad design pcb/motor.kicad_sch (2026-06-30)

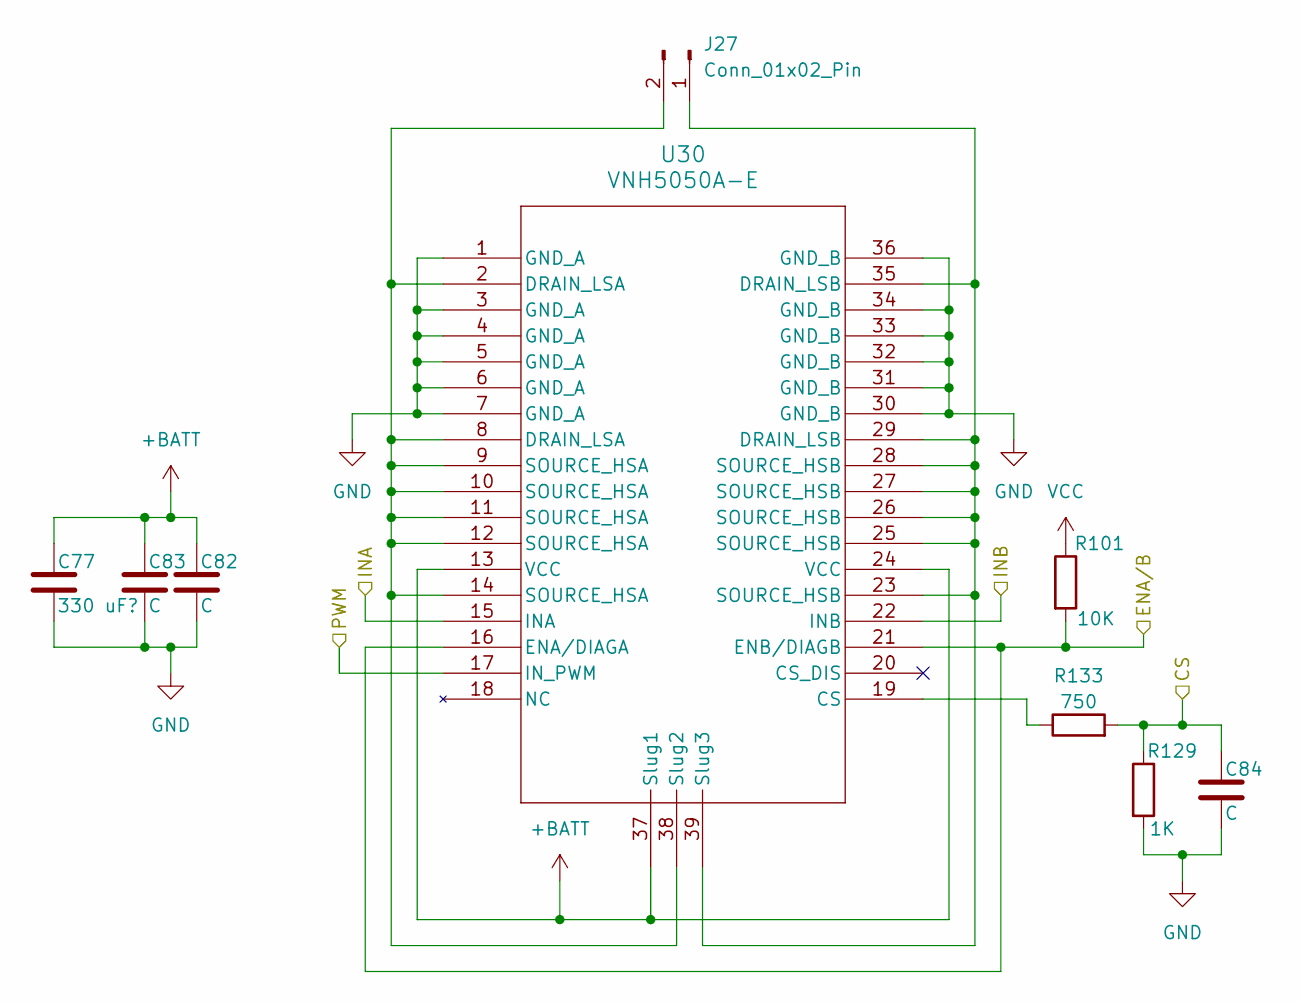
[picture p21: schematic motor.kicad_sch]

Parts:
C77: 330 uF?
C82, C83, C84: C
J27: Conn_01x02_Pin
R101: 10K
R129: 1K
R133: 750
U30: VNH5050A-E; SOIC_050A-E_STM

Connections:
+BATT: C77.1, C82.1, C83.1, U30.13 (VCC), U30.24 (VCC), U30.37 (Slug1)
CS: C84.1, R129.1, R133.2
ENA/B: R101.2, U30.16 (ENA/DIAGA), U30.21 (ENB/DIAGB)
GND: C77.2, C82.2, C83.2, C84.2, R129.2, U30.1 (GND_A), U30.3 (GND_A), U30.4 (GND_A), U30.5 (GND_A), U30.6 (GND_A), U30.7 (GND_A), U30.30 (GND_B), U30.31 (GND_B), U30.32 (GND_B), U30.33 (GND_B), U30.34 (GND_B), U30.36 (GND_B)
INA: U30.15 (INA)
INB: U30.22 (INB)
unnamed: J27.1, U30.23 (SOURCE_HSB), U30.25 (SOURCE_HSB), U30.26 (SOURCE_HSB), U30.27 (SOURCE_HSB), U30.28 (SOURCE_HSB), U30.29 (DRAIN_LSB), U30.35 (DRAIN_LSB), U30.39 (Slug3)
unnamed: J27.2, U30.2 (DRAIN_LSA), U30.8 (DRAIN_LSA), U30.9 (SOURCE_HSA), U30.10 (SOURCE_HSA), U30.11 (SOURCE_HSA), U30.12 (SOURCE_HSA), U30.14 (SOURCE_HSA), U30.38 (Slug2)
unnamed: R133.1, U30.19 (CS)
PWM: U30.17 (IN_PWM)
VCC: R101.1
