tonyxforce/LynxSchematic/pcb/motors.kicad_sch

## KiCad design pcb/motors.kicad_sch (2026-06-30)

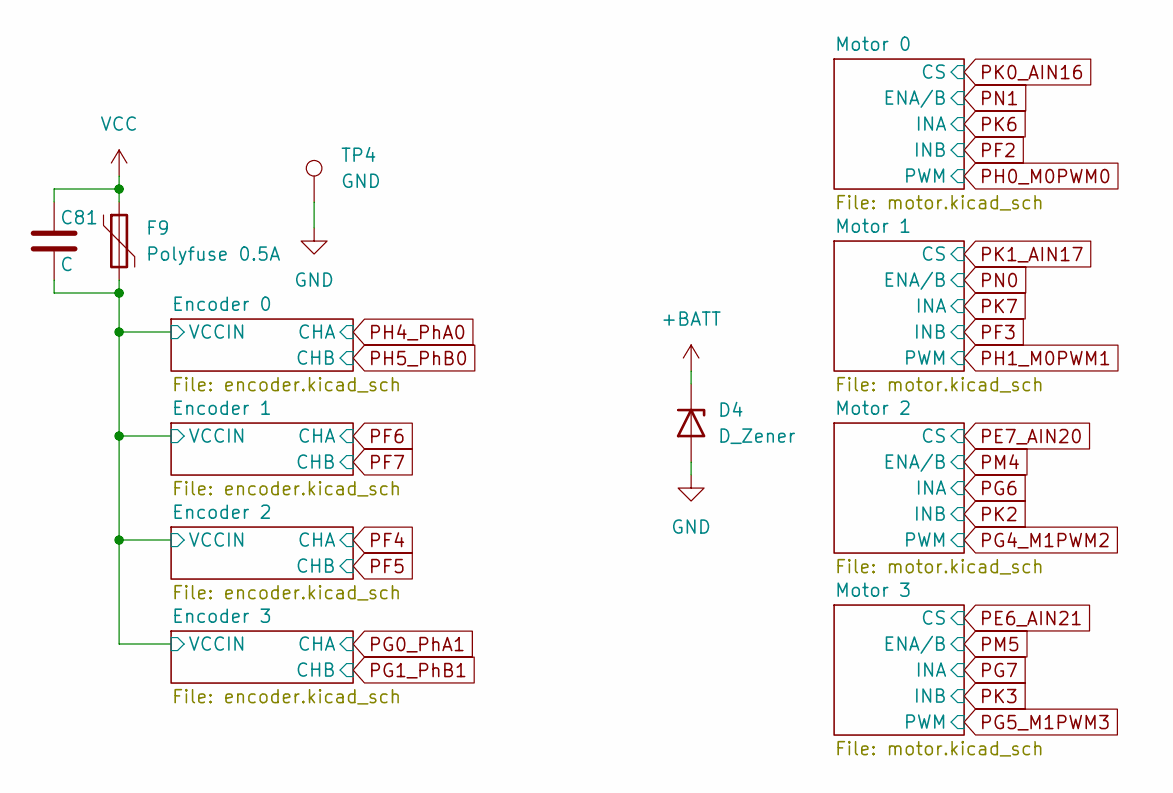
[picture p22: schematic motors.kicad_sch]

Parts:
C81: C
D4: D_Zener
F9: Polyfuse 0.5A
TP4: GND

Connections:
+BATT: D4.1 (K)
GND: D4.2 (A), TP4.1
VCC: C81.2, F9.1
VCCIN: C81.1, F9.2
