tonyxforce/LynxSchematic/pcb/rs485.kicad_sch

## KiCad design pcb/rs485.kicad_sch (2026-06-30)

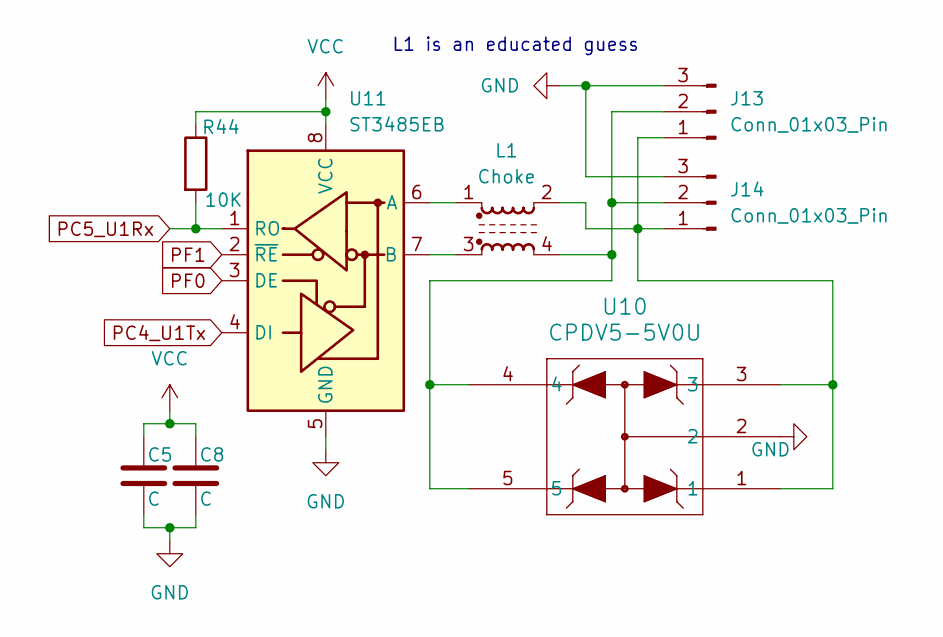
[picture p23: schematic rs485.kicad_sch]

Parts:
C5, C8: C
J13, J14: Conn_01x03_Pin
L1: Choke
R44: 10K
U10: CPDV5-5V0U; SOT353_CPDV5_CIP
U11: ST3485EB; SOIC-8_3.9x4.9mm_P1.27mm

Connections:
GND: C5.2, C8.2, J13.3, J14.3, U10.2, U11.5 (GND)
unnamed: J13.1, J14.1, L1.2, U10.1, U10.3
unnamed: J13.2, J14.2, L1.4, U10.4, U10.5
unnamed: L1.1, U11.6 (A)
unnamed: L1.3, U11.7 (B)
PC4_U1Tx: U11.4 (DI)
PC5_U1Rx: R44.2, U11.1 (RO)
PF0: U11.3 (DE)
PF1: U11.2 (~RE)
VCC: C5.1, C8.1, R44.1, U11.8 (VCC)

Notes on the sheet:
L1 is an educated guess
