tonyxforce/LynxSchematic/pcb/servo.kicad_sch

## KiCad design pcb/servo.kicad_sch (2026-06-30)

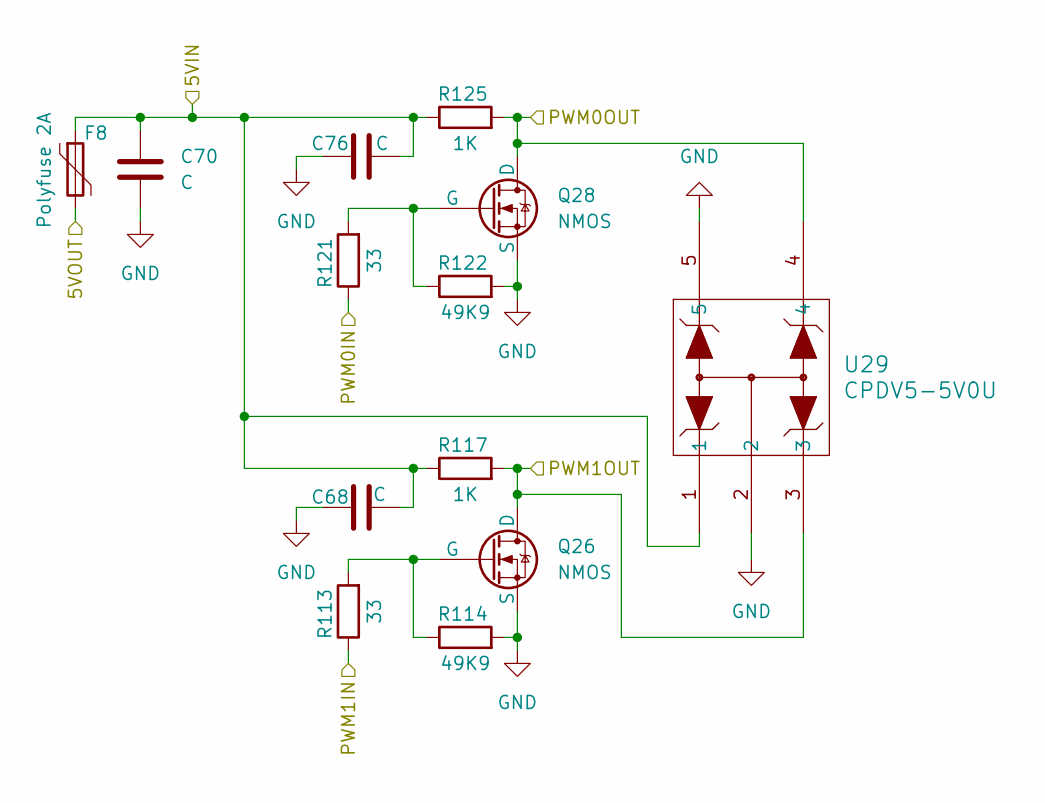
[picture p24: schematic servo.kicad_sch]

Parts:
C68, C70, C76: C
F8: Polyfuse 2A
Q26, Q28: NMOS
R113, R121: 33
R114, R122: 49K9
R117, R125: 1K
U29: CPDV5-5V0U; SOT353_CPDV5_CIP

Connections:
5VIN: C68.2, C70.1, C76.2, F8.1, R117.1, R125.1, U29.1
5VOUT: F8.2
GND: C68.1, C70.2, C76.1, Q26.3 (S), Q28.3 (S), R114.2, R122.2, U29.2, U29.5
unnamed: Q26.2 (G), R113.2, R114.1
unnamed: Q28.2 (G), R121.2, R122.1
PWM0IN: R121.1
PWM0OUT: Q28.1 (D), R125.2, U29.4
PWM1IN: R113.1
PWM1OUT: Q26.1 (D), R117.2, U29.3
