tonyxforce/LynxSchematic/pcb/usb.kicad_sch

## KiCad design pcb/usb.kicad_sch (2026-06-30)

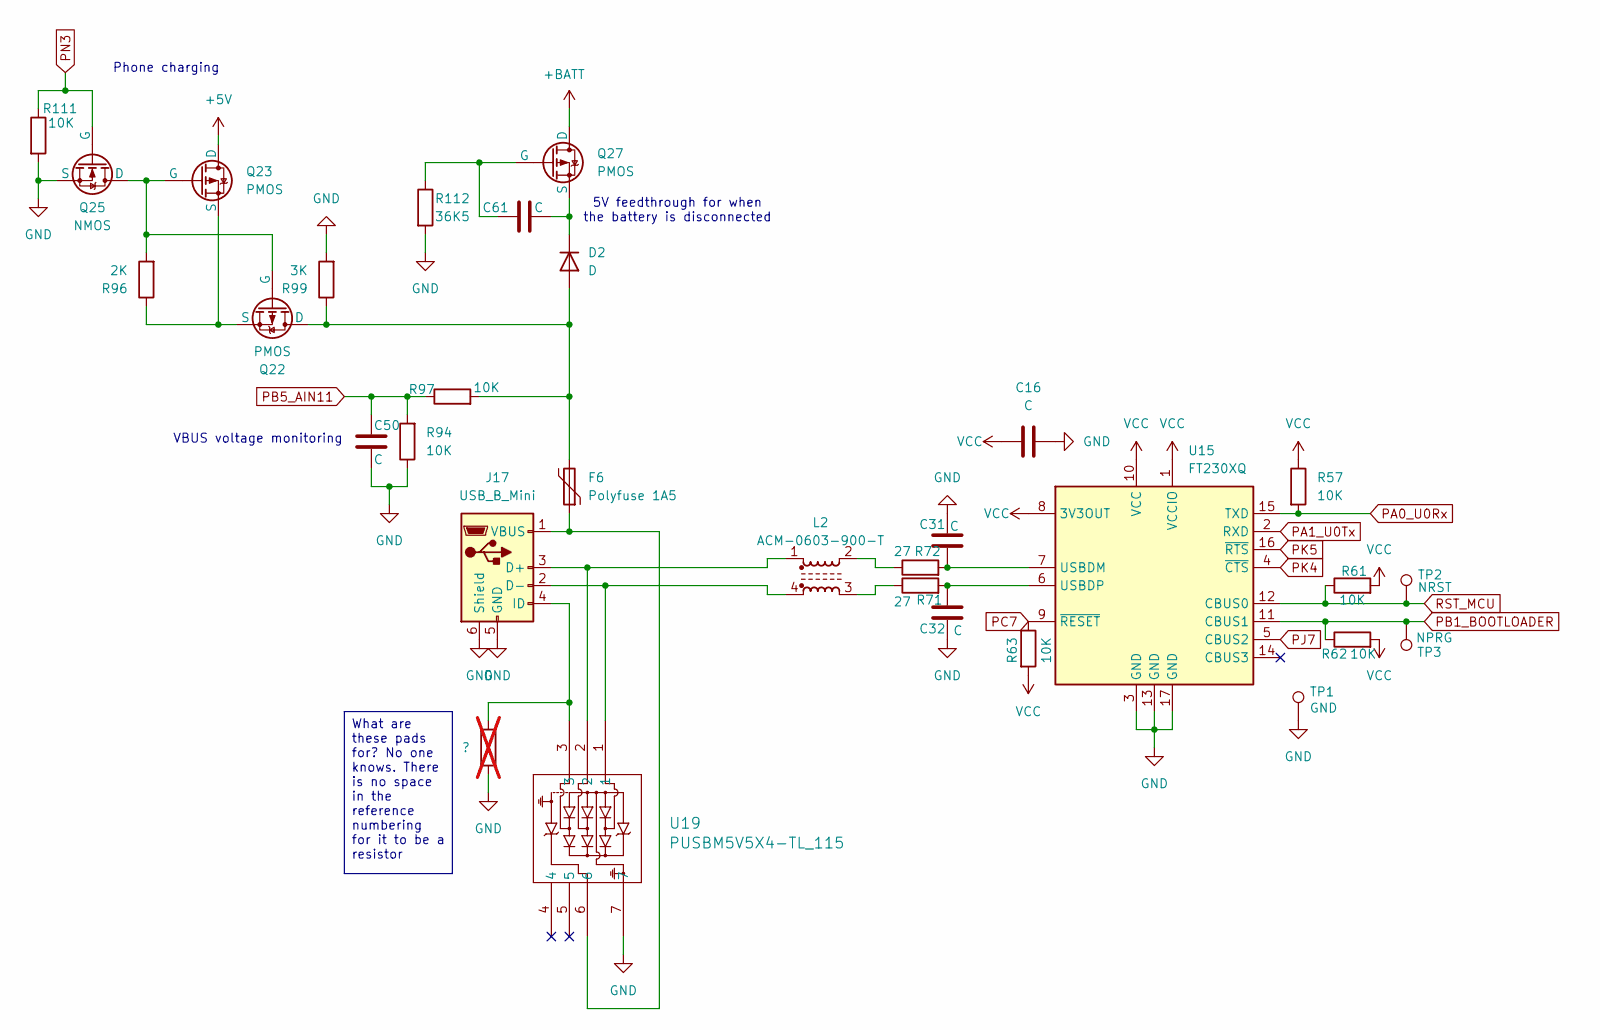
[picture p25: schematic usb.kicad_sch]

Parts:
C16, C31, C32, C50, C61: C
D2: D
F6: Polyfuse 1A5
J17: USB_B_Mini
L2: ACM-0603-900-T; L_CommonModeChoke_Coilcraft_0603USB
Q22, Q23, Q27: PMOS
Q25: NMOS
R57, R61, R62, R63, R94, R97, R111: 10K
R71, R72: 27
R96: 2K
R99: 3K
R112: 36K5
TP1: GND
TP2: NRST
TP3: NPRG
U15: FT230XQ; QFN-16-1EP_4x4mm_P0.65mm_EP2.1x2.1mm
U19: PUSBM5V5X4-TL_115; DFN1616-6_SOT1189-1_NEX

Connections:
+5V: Q23.1 (D)
+BATT: Q27.1 (D)
GND: C16.2, C31.1, C32.2, C50.2, J17.5 (GND), J17.6 (Shield), Q25.3 (S), R94.1, R99.2, R111.2, R112.2, TP1.1, U15.3 (GND), U15.13 (GND), U15.17 (GND), U19.7
unnamed: C31.2, R72.2, U15.7 (USBDM)
unnamed: C32.1, R71.2, U15.6 (USBDP)
unnamed: C61.1, Q27.2 (G), R112.1
unnamed: C61.2, D2.1 (K), Q27.3 (S)
unnamed: D2.2 (A), F6.2, Q22.1 (D), R97.2, R99.1
unnamed: F6.1, J17.1 (VBUS), U19.6
unnamed: J17.2 (D-), L2.4, U19.1
unnamed: J17.3 (D+), L2.1, U19.2
unnamed: J17.4 (ID), U19.3
unnamed: L2.2, R72.1
unnamed: L2.3, R71.1
unnamed: Q22.2 (G), Q23.2 (G), Q25.1 (D), R96.2
unnamed: Q22.3 (S), Q23.3 (S), R96.1
PA0_U0Rx: R57.2, U15.15 (TXD)
PA1_U0Tx: U15.2 (RXD)
PB1_BOOTLOADER: R62.1, TP3.1, U15.11 (CBUS1)
PB5_AIN11: C50.1, R94.2, R97.1
PC7: R63.1, U15.9 (~RESET)
PJ7: U15.5 (CBUS2)
PK4: U15.4 (~CTS)
PK5: U15.16 (~RTS)
PN3: Q25.2 (G), R111.1
RST_MCU: R61.1, TP2.1, U15.12 (CBUS0)
VCC: C16.1, R57.1, R61.2, R62.2, R63.2, U15.1 (VCCIO), U15.8 (3V3OUT), U15.10 (VCC)

Notes on the sheet:
VBUS voltage monitoring
5V feedthrough for when the battery is disconnected
Phone charging
What are these pads for? No one knows. There is no space in the reference numbering for it to be a resistor
