tonyxforce/LynxSchematic/pcb/vrefa_plus.kicad_sch

## KiCad design pcb/vrefa_plus.kicad_sch (2026-06-30)

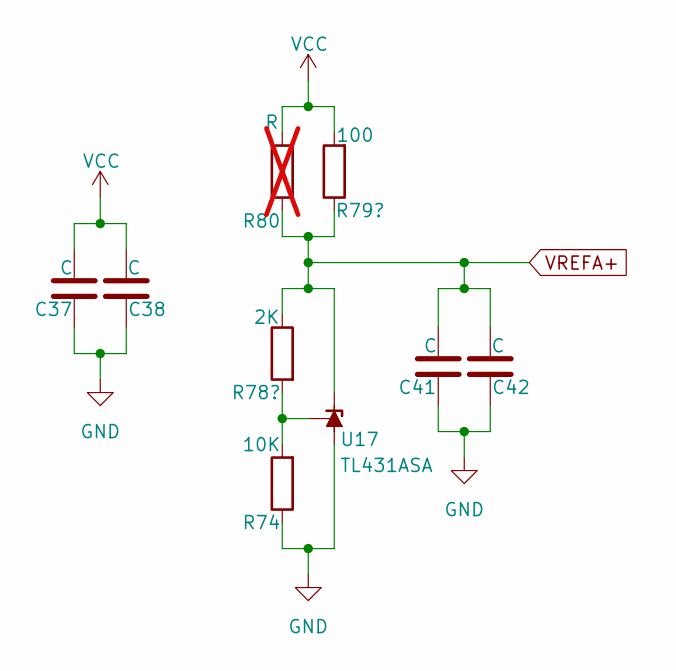
[picture p26: schematic vrefa_plus.kicad_sch]

Parts:
C37, C38, C41, C42: C
R74: 10K
R80: R; not fitted
U17: TL431ASA; SOT-23

Connections:
GND: C37.2, C38.2, C41.1, C42.1, R74.1, U17.3 (A)
unnamed: R74.2, U17.2 (REF)
VCC: C37.1, C38.1, R80.2
VREFA+: C41.2, C42.2, R80.1, U17.1 (K)
